mkulesh/avrDigitalClock/images/display_board1.jpg

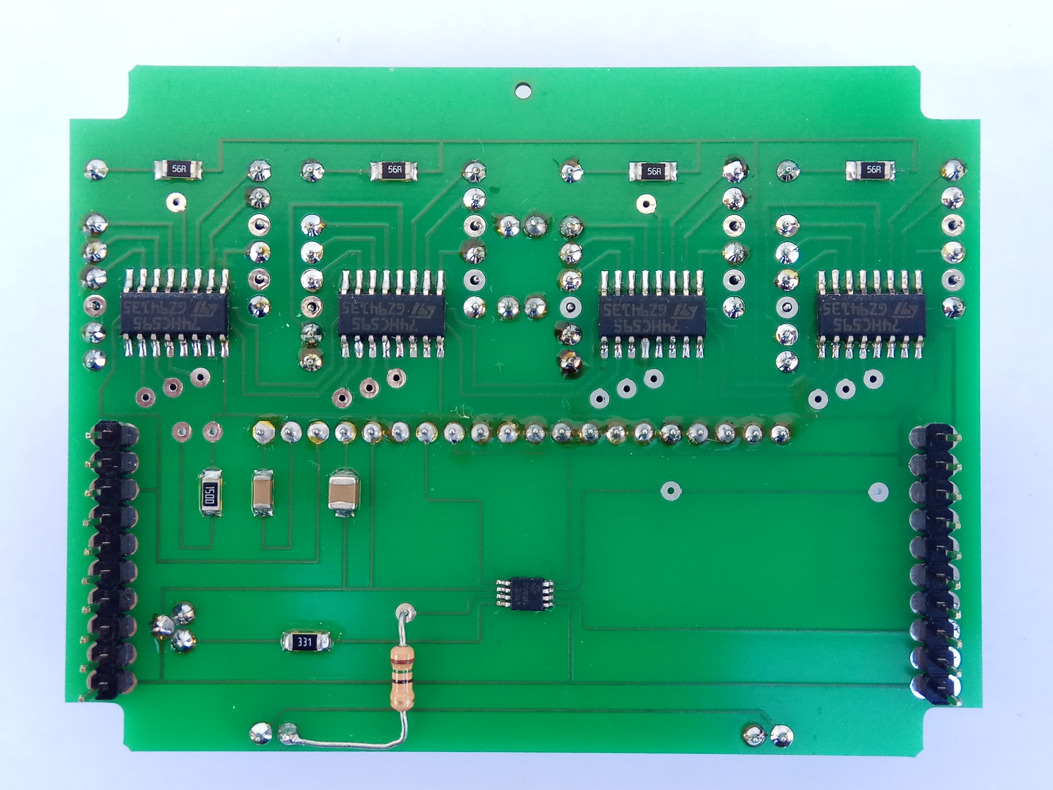
images/display_board1.jpg
