mkulesh/avrDigitalClock/images/on_breadboard2.jpg

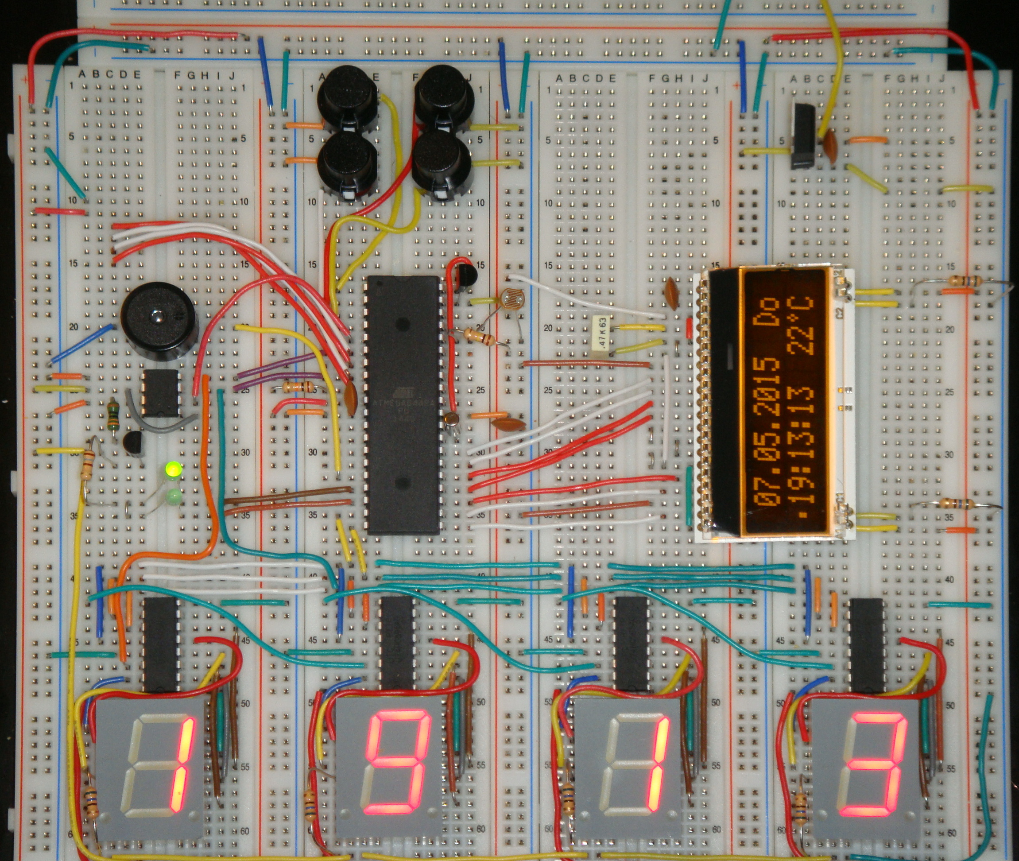
images/on_breadboard2.jpg
