mkulesh/avrDigitalClock/images/programming.jpg

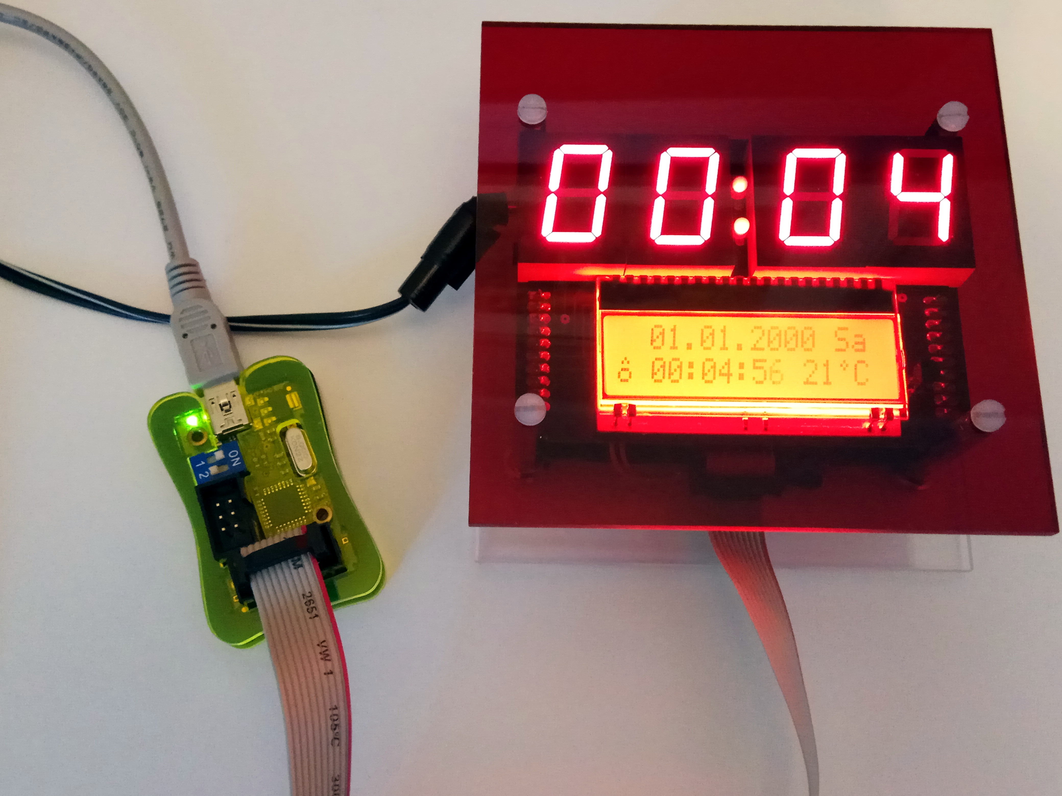
images/programming.jpg
