mkulesh/avrDigitalClock/images/all_parts.jpg

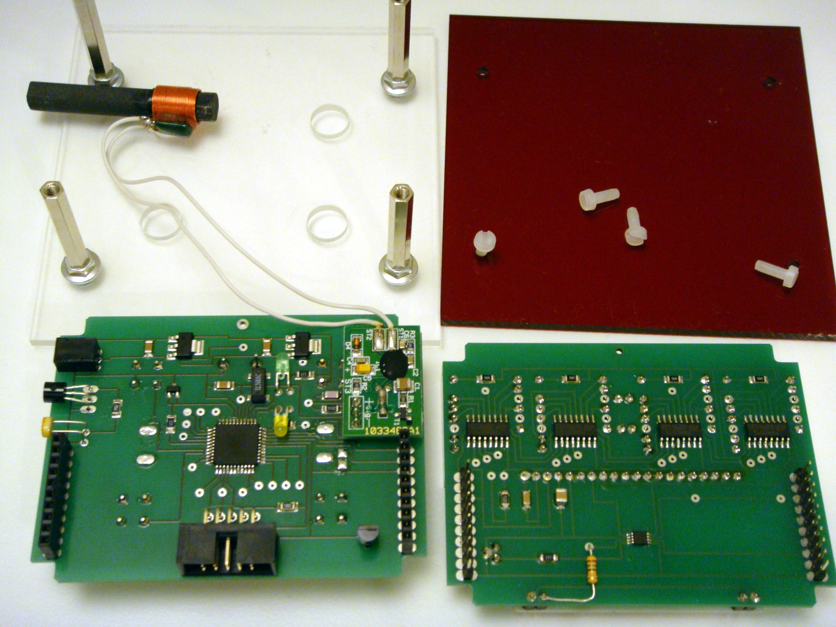
images/all_parts.jpg
