mkulesh/avrDigitalClock/src/Screens.h

/*******************************************************************************
 * avrDigitalClock - a digital clock based on ATmega644 MCU
 * *****************************************************************************
 * Copyright (C) 2014-2017 Mikhail Kulesh
 * 
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
 * You should have received a copy of the GNU General Public License
 * along with this program.  If not, see <http://www.gnu.org/licenses/>.
 ******************************************************************************/

#ifndef SCREENS_H_
#define SCREENS_H_

#include "AvrPlusPlus/Time.h"

// Interface for display data provider
class DisplayDataProvider
{
public:
    virtual const AvrPlusPlus::tm & getDayTime() const = 0;
    virtual bool isAlarmActive() const = 0;
    virtual bool isActiveElementVisible() const = 0;
    virtual bool isDcfTimeAvailable() const = 0;
    virtual float getTemperature() const = 0;
};

// Basic class for a display screen
class Screen
{
public:
    virtual void setFirst() = 0;
    virtual void setNext() = 0;
    virtual void fillLine(int line, const DisplayDataProvider * dataProvider, char * dest) = 0;
};

// Class describing the home screen
class HomeScreen: public Screen
{
public:
    HomeScreen()
    {
    };
    void setFirst()
    {
    };
    void setNext()
    {
    };
    void fillLine(int line, const DisplayDataProvider * dataProvider, char * dest);
};

// Class describing the state of time setting screen
class TimeSetting: public Screen
{
public:
    enum Element
    {
        TS_DAY = 0, TS_MONTH = 1, TS_YEAR = 2, TS_HOUR = 3, TS_MIN = 4, TS_SEC = 5
    };

    TimeSetting() : activeElement(TS_DAY)
    {
    };
    inline void setFirst()
    {
        activeElement = TS_DAY;
    };
    inline void setActiveElement(Element element)
    {
        activeElement = element;
    };
    void setNext();
    void fillLine(int line, const DisplayDataProvider * dataProvider, char * dest);
    void modifyValue(AvrPlusPlus::tm & dayTime, int s);

private:
    static const unsigned char elementPos[6][3];
    Element activeElement;
};

// Class describing the state of brightness setting screen
class BrightnessSetting: public Screen
{
public:
    enum Element
    {
        BS_MODE = 0, BS_MAN_VALUE = 1
    };

    typedef struct
    {
        bool isManual;
        unsigned char manValue;
    } Data;

    BrightnessSetting();
    inline bool isManual()
    {
        return data.isManual;
    };
    inline unsigned char manValue()
    {
        return data.manValue;
    };
    void setFirst();
    void setNext();
    void fillLine(int line, const DisplayDataProvider * dataProvider, char * dest);
    void modifyValue(int s);

private:
    static const unsigned char elementPos[2][3];
    Element activeElement;
    Data data;
};

// Class describing the state of alarm setting screen
class AlarmSetting: public Screen
{
public:
    enum Element
    {
        AS_ACTIVE = 0,
        AS_HOUR = 1,
        AS_MIN = 2,
        AS_DAY1 = 3,
        AS_DAY2 = 4,
        AS_DAY3 = 5,
        AS_DAY4 = 6,
        AS_DAY5 = 7,
        AS_DAY6 = 8,
        AS_DAY7 = 9
    };

    typedef struct
    {
        bool isActive;
        int8_t hour;
        int8_t min;
        bool days[7];
    } Data;

    AlarmSetting(unsigned char _number);
    inline bool isActive() const
    {
        return data.isActive;
    };
    void setFirst();
    void setNext();
    void fillLine(int line, const DisplayDataProvider * dataProvider, char * dest);
    void modifyValue(int s);
    bool isOccured(const AvrPlusPlus::tm & dayTime) const;

private:
    static const unsigned char elementPos[10][3];
    Element activeElement;
    static const char * activeString[2];
    unsigned char number;
    Data data;
};

#endif
